TheChatou/42Hero/docs/42Hero/Diffuseur3.png

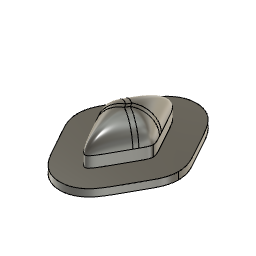
docs/42Hero/Diffuseur3.png
