TheChatou/42Hero/code/mario.h

/* ************************************************************************** */
/*                                                                            */
/*                                                        :::      ::::::::   */
/*   mario.h                                            :+:      :+:    :+:   */
/*                                                    +:+ +:+         +:+     */
/*   By: lmahe <lmahe@student.42.fr>                +#+  +:+       +#+        */
/*                                                +#+#+#+#+#+   +#+           */
/*   Created: 2025/06/18 18:48:59 by chatou            #+#    #+#             */
/*   Updated: 2025/08/04 09:14:43 by lmahe            ###   ########.fr       */
/*                                                                            */
/* ************************************************************************** */


#ifndef MARIO_TEST_H
#define MARIO_TEST_H

#include "parts.h"

const t_part mario_test PROGMEM = {
    .tracks = {
        { .note = { 0,0,0,0,0,0,0,659, 659, 659, 659, 0, 523, 523, 659, 659, 784, 784, 784, 784, 0, 0, 0, 0, 0, 0, 523, 523, 523, 392, 0, 0, 0, 330, 330, 0, 440, 440, 440, 494, 0, 466, 440, 440, 440, 392, 659, 659, 784, 880, 880, 880, 698, 784, 0, 659, 659, 659, 523, 587, 494, 494, 494, 494, 523, 52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
        { .note = { 0,0,0,0,0,0,0,370, 370, 370, 370, 0, 370, 370, 370, 370, 494, 494, 494, 494, 0, 392, 392, 392, 392, 0, 330, 330, 330, 262, 0, 0, 0, 196, 196, 0, 262, 262, 262, 294, 0, 277, 262, 262, 262, 262, 392, 392, 494, 523, 523, 523, 440, 494, 0, 440, 440, 440, 330, 349, 294, 294, 294, 294,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
        { .note = { 0,0,0,0,0,0,0,147, 147, 147, 147, 0, 147, 147, 147, 147, 392, 392, 392, 392, 0, 196, 196, 196, 196, 0, 196, 196, 196, 165, 0, 0, 0, 131, 131, 0, 175, 175, 175, 196, 0, 185, 175, 175, 175, 165, 262, 262, 330, 349, 349, 349, 294, 330, 0, 262, 262, 262, 220, 247, 196, 196, 196, 196, 196, 196, 196, 165, 0, 0, 0, 131, 131, 0, 175, 175, 175, 196, 0, 185, 175, 175, 175, 165, 262, 262, 330, 349, 349, 349, 294, 330, 0, 262, 262, 262, 220, 247, 196, 196, 196, 196, 131, 131, 131, 196, 0, 0, 0, 262, 262, 175, 175, 175, 175, 262, 262, 262, 175, 175, 175, 131, 131, 131, 165, 0, 0, 0, 196, 262, 0, 784, 784, 784, 784, 784, 784, 196, 196, 196, 131, 131, 131, 196, 196, 0, 0, 262, 262, 175, 175, 175, 175, 262, 262, 262, 175, 175, 175, 131, 131, 208, 208, 208, 0, 233, 233, 233, 262, 262, 262, 262, 196, 196, 196, 0, 131, 131, 131, 131, 131, 196, 196, 0, 0, 262, 262, 175, 175, 175, 175, 262, 262, 262, 262, 175, 175, 131, 131, 131, 0, 165, 0, 0, 196, 262, 0, 0, 784, 784, 784, 784, 784, 784, 196, 196, 131, 131, 131, 131, 196, 0, 0, 262, 262, 0, 175, 175, 175, 262, 262, 262, 262, 175, 175, 131, 131, 208, 208, 208, 0, 233, 233, 233, 233, 262, 262, 262, 196, 196, 196, 196, 131, 131, 104, 104, 104, 104, 156, 0, 0, 208, 208, 208, 196, 196, 196, 131, 0, 0, 0, 98, 98, 104, 104, 104, 104, 156, 0, 0, 208, 208, 208, 196, 196, 196, 131, 0, 0, 0, 98, 98, 104, 104, 104, 104, 156, 0, 0, 208, 208, 208, 196, 196, 196, 131, 0, 0, 0, 98, 98, 147, 147, 147, 147, 147, 0, 147, 147, 147, 147, 392, 392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
    .tempo = 300,
    .length = 762,
    .diff = { 3, 1 }
};



#endif
