TheChatou/42Hero/code/sonic.h

#ifndef SONIC_H
#define SONIC_H

#include "parts.h"

const t_part sonic PROGMEM = {
    .tracks = {
        { .note = { 698, 880, 698, 988, 784, 784, 1047, 880, 1047, 880, 1175, 1175, 988, 1319, 1047, 1319, 1047, 1047, 1319, 1047, 1319, 1047, 1319, 1319, 1047, 1319, 1047, 1319, 1047, 1047, 1319, 1047, 1319, 1047, 1319, 1319, 0, 0, 0, 0, 0, 0, 0, 0, 0, 0, 0, 0, 0, 0, 0, 0, 0, 0, 0, 0, 0, 0, 0, 0, 0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
        { .note = { 0, 110, 110, 220, 220, 110, 117, 117, 233, 233, 123, 247, 247, 131, 0, 0, 0, 0, 131, 0, 131, 0, 0, 131, 0, 131, 0, 0, 0, 0, 131, 0, 131, 0, 0, 131, 0, 131, 0, 0, 0, 0, 131, 0, 131, 0, 0, 131, 0, 131, 0, 0, 0, 0, 131, 131, 131, 131, 110, 110, 110, 117, 117, 117, 117, 123, 123, 123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
        { .note = { 0, 0, 0, 0, 0, 0, 0, 0, 0, 0, 0, 0, 0, 330, 330, 330, 330, 330, 294, 294, 294, 294, 294, 330, 330, 330, 330, 330, 330, 294, 294, 294, 294, 294, 330, 330, 330, 294, 294, 294, 294, 349, 349, 349, 349, 349, 330, 330, 330, 330, 330, 294, 294, 294, 294, 294, 294, 294, 294, 294, 294, 2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
        { .note = { 0, 0, 0, 0, 0, 0, 0, 0, 0, 0, 0, 0, 0, 0, 0, 0, 0, 0, 0, 0, 0, 0, 0, 0, 0, 0, 0, 0, 0, 0, 0, 0, 0, 0, 0, 0, 0, 0, 0, 0, 0, 0, 0, 0, 0, 0, 0, 0, 0, 0, 0, 0, 0, 0, 0, 0, 0, 0, 0, 0, 0, 0, 0, 0, 0, 0, 0, 0, 0, 0, 0, 0, 0, 0, 0, 0, 0, 0, 0, 0, 0, 0, 0, 0, 0, 0, 0, 0, 0, 0, 0, 0, 0, 0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
    },
    .led = { 1, 3, 3, 3, 3, 3, 3, 3, 3, 3, 3, 3, 3, 7, 5, 5, 5, 5, 7, 5, 7, 5, 5, 7, 5, 7, 5, 5, 5, 5, 7, 5, 7, 5, 5, 7, 4, 6, 4, 4, 4, 4, 6, 4, 6, 4, 4, 6, 4, 6, 4, 4, 4, 4, 6, 6, 6, 6, 6, 6, 6, 6, 6, 6, 6, 6, 6, 6, 6, 4, 4, 6, 4, 6, 4, 4, 4, 4, 6, 4, 6, 4, 4, 6, 4, 6, 4, 4, 4, 4, 6, 4, 6, 4, 4, 6, 4, 6, 4, 4, 4, 4, 6, 4, 6, 4, 4, 6, 4, 6, 4, 4, 4, 4, 6, 4, 6, 4, 6, 6, 6, 6, 6, 0, 0, 0, 6, 4, 2, 0, 9, 15, 13, 11, 0, 9, 9, 9, 11, 0, 15, 13, 9, 11, 9, 15, 15, 11, 11, 11, 11, 9, 11, 9, 13, 11, 9, 11, 9, 13, 13, 9, 11, 9, 11, 9, 9, 15, 13, 11, 9, 9, 0, 15, 11, 11, 11, 11, 9, 11, 9, 15, 13, 9, 0, 9, 15, 13, 11, 0, 9, 11, 9, 11, 0, 13, 13, 9, 11, 0, 15, 13, 9, 11, 9, 11, 9, 9, 9, 13, 11, 9, 11, 9, 13, 11, 9, 11, 9, 9, 9, 9, 15, 13, 11, 9, 9, 15, 15, 11, 11, 11, 11, 9, 11, 9, 15, 13, 9, 11, 9, 15, 13, 9, 0, 9, 11, 9, 11, 0, 13, 11, 9, 11, 0, 15, 15, 11, 11, 11, 11, 9, 9, 15, 13, 11, 9, 9, 9, 13, 11, 0, 11, 9, 9, 11, 9, 15, 13, 9, 9, 9, 15, 15, 11, 11, 11, 11, 9, 11, 9, 13, 13, 0, 11, 9, 15, 13, 9, 11, 9, 11, 9, 9, 0, 13, 11, 9, 11, 0, 13, 11, 9, 11, 9, 9, 9, 9, 15, 4, 11, 9, 9, 15, 13, 11, 0, 9, 9, 9, 11, 0, 15, 13, 9, 11, 9, 15, 13, 9, 9, 9, 15, 15, 15, 15, 15, 15, 15, 15, 15, 15, 13, 15, 15, 15, 15, 15, 15, 15, 15, 15, 13, 15, 13, 13, 15, 15, 15, 13, 15, 15, 15, 15, 13, 15, 15, 15, 15, 13, 15, 15, 15, 15, 15, 15, 15, 15, 15, 15, 15, 13, 13, 13, 15, 15, 13, 15, 15, 15, 15, 15, 15, 15, 15, 15, 15, 15, 15, 15, 15, 15, 15, 15, 15, 15, 15, 13, 15, 13, 13, 15, 15, 15, 13, 15, 15, 15, 15, 4, 15, 15, 15, 15, 13, 15, 6, 15, 11, 11, 15, 15, 15, 15, 15, 15, 15, 15, 15, 15, 15, 15, 2, 0, 0, 6, 4, 2, 0, 9, 9, 13, 11, 0, 11, 9, 9, 11, 9, 15, 13, 9, 9, 9, 15, 15, 11, 11, 11, 11, 9, 11, 9, 13, 4, 9, 11, 9, 15, 13, 9, 11, 9, 11, 9, 9, 0, 13, 11, 9, 11, 0, 15, 11, 11, 11, 11, 9, 9, 9, 15, 13, 11, 0, 9, 15, 13, 11, 0, 9, 9, 9, 11, 0, 15, 13, 9, 11, 9, 15, 13, 9, 9, 9, 11, 9, 11, 9, 13, 11, 9, 11, 9, 13, 13, 9, 11, 9, 11, 9, 9, 15, 13, 11, 9, 9, 0, 15, 11, 11, 11, 11, 9, 11, 9, 15, 13, 9, 0, 9, 15, 13, 11, 0, 9, 11, 9, 11, 0, 13, 13, 9, 11, 0, 15, 15, 11, 11, 11, 11, 9, 9, 9, 13, 11, 9, 11, 9, 13, 11, 9, 11, 9, 9, 9, 9, 15, 13, 11, 9, 9, 15, 15, 11, 11, 11, 11, 9, 11, 9, 15, 13, 9, 11, 9, 15, 13, 9, 0, 9, 11, 9, 11, 0, 13, 11, 9, 11, 0, 13, 13, 9, 11, 9, 11, 9, 9, 15, 13, 11, 9, 9, 9, 13, 11, 0, 11, 9, 9, 11, 9, 15, 13, 9, 9, 9, 15, 13, 11, 9, 9, 15, 15, 15, 15, 15, 13, 15, 15, 15, 15, 13, 15, 15, 15, 15, 15, 15, 15, 15, 15, 13, 15, 13, 13, 15, 15, 15, 13, 15, 15, 15, 15, 13, 15, 15, 15, 15, 15, 15, 15, 15, 15, 15, 15, 15, 15, 15, 15, 15, 13, 13, 13, 15, 15, 13, 15, 15, 15, 15, 15, 15, 15, 15, 15, 15, 13, 15, 15, 15, 15, 15, 15, 15, 15, 15, 13, 15, 13, 13, 15, 15, 15, 13, 15, 15, 15, 15, 4, 15, 15, 15, 15, 13, 15, 6, 15, 11, 11, 15, 15, 15, 15, 15, 15, 15, 15, 15, 15, 15, 15, 0 },
    .tempo = 300,
    .length = 782,
    .diff = { 4, 0 }
};


#endif
