TheChatou/42Hero/code/tetris.h

#ifndef TETRIS_TEST_H
#define TETRIS_TEST_H

#include "parts.h"

const t_part tetris_test PROGMEM = {
    .tracks = {
        { .note = { 0, 0, 0, 0, 0, 0, 0, 659, 659, 659, 659, 494, 494, 523, 523, 587, 587, 659, 587, 523, 523, 494, 494, 440, 440, 440, 440, 440, 440, 523, 523, 659, 659, 659, 659, 587, 587, 523, 523, 494, 494, 494, 494, 494, 494, 523, 523, 587, 587, 587, 587, 659, 659, 659, 659, 523, 523, 523, 523,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
        { .note = { 0, 0, 0, 0, 0, 0, 0, 494, 494, 494, 494, 415, 415, 440, 440, 494, 494, 494, 494, 440, 440, 415, 415, 330, 330, 330, 330, 330, 330, 440, 440, 523, 523, 523, 523, 494, 494, 440, 440, 415, 415, 330, 330, 415, 415, 440, 440, 494, 494, 494, 494, 523, 523, 523, 523, 440, 440, 440, 440,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
        { .note = { 0, 0, 0, 0, 0, 0, 0, 82, 82, 165, 165, 82, 82, 165, 165, 82, 82, 165, 165, 82, 82, 165, 165, 110, 110, 220, 220, 110, 110, 220, 220, 110, 110, 220, 220, 110, 110, 220, 220, 104, 104, 208, 208, 104, 104, 208, 208, 82, 82, 165, 165, 82, 82, 165, 165, 110, 110, 220, 220, 110, 110, 220, 220, 110, 110, 220, 220, 123, 123, 131, 131, 147, 147, 73, 73, 0, 0, 73, 73, 0, 0, 73, 73, 110, 110, 87, 87, 65, 65, 131, 131, 0, 0, 131, 131, 65, 65, 98, 98, 98, 98, 0, 0, 123, 123, 247, 247, 0, 0, 247, 247, 0, 0, 165, 165, 0, 0, 208, 208, 110, 110, 165, 165, 110, 110, 165, 165, 110, 110, 110, 110, 0, 0, 0, 0, 82, 82, 165, 165, 82, 82, 165, 165, 82, 82, 165, 165, 82, 82, 165, 165, 110, 110, 220, 220, 110, 110, 220, 220, 110, 110, 220, 220, 110, 110, 220, 220, 104, 104, 208, 208, 104, 104, 208, 208, 82, 82, 165, 165, 82, 82, 165, 165, 110, 110, 220, 220, 110, 110, 220, 220, 110, 110, 220, 220, 123, 123, 131, 131, 147, 147, 73, 73, 0, 0, 73, 73, 0, 0, 73, 73, 110, 110, 87, 87, 65, 65, 131, 131, 0, 0, 131, 131, 65, 65, 98, 98, 98, 98, 0, 0, 123, 123, 247, 247, 0, 0, 247, 247, 0, 0, 165, 165, 0, 0, 208, 208, 110, 110, 165, 165, 110, 110, 165, 165, 110, 110, 110, 110, 0, 0, 0, 0, 220, 220, 330, 330, 220, 220, 330, 330, 220, 220, 330, 330, 220, 220, 330, 330, 208, 208, 330, 330, 208, 208, 330, 330, 208, 208, 330, 330, 208, 208, 330, 330, 220, 220, 330, 330, 220, 220, 330, 330, 220, 220, 330, 330, 220, 220, 330, 330, 208, 208, 330, 330, 208, 208, 330, 330, 0, 0, 0, 0, 0, 0, 0, 0, 220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
    .tempo = 300,
    .length = 648,
    .diff = { 4, 0 }
};

// rythm 1
// rythm + first 3
// rythm + second 5
// rythm + third 9

//440-586
// 586-732
// 732+


#endif
