TheChatou/42Hero/code/zelda.h

#ifndef ZELDA_H
#define ZELDA_H


#include "parts.h"


const t_part zelda PROGMEM = {
    .tracks = {
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
    0, 0, 0, 0, 14, 14, 14, 2, 2, 0, 13, 13, 13, 13, 13, 13, 
    13, 5, 5, 5, 10, 10, 10, 10, 10, 10, 0, 0, 0, 8, 2, 11, 
    11, 8, 12, 12, 12, 0, 0, 12, 0, 12, 0, 12, 12, 0, 0, 0, 0, 0, 0, 0, 0, 0
},
    .tempo = 350,
    .length = 319,
    .diff = { 4, 0 }
};


#endif
