TheChatou/42Hero/code/expander.h

#ifndef EXPANDER_H
#define EXPANDER_H

#include <avr/io.h>
#include <util/delay.h>
#include <stdbool.h>
/* 
expander/shift-register datasheet : https://www.ti.com/lit/ds/symlink/sn74hc595.pdf
 */


/// @brief struct that represent the first of a linear sequence of expanders
typedef struct Expander
{
    volatile uint8_t    *port;
    uint8_t             rclck; // 12
    uint8_t             srclk; // 11
    uint8_t             ser; // 14

} Expander;

void    shiftLane(volatile Expander *exp, volatile uint8_t *lane, uint8_t size);
void    turn_leds_off();
void    turn_leds_on();


#endif
